arwidcool/Solder-Plate/src/thermistors/ThermistorLookup.h

#ifndef THERMISTOR_LOOKUP_H
#define THERMISTOR_LOOKUP_H

#include <Arduino.h>
#include <common.h>

struct LookupEntry
{
    uint8_t temperature;
    float value;
};

const LookupEntry lookupBottomMiddle[] = {


// {0, 1},
// {25, 1.00715513834484},
// {35, 1.12484607155925},
// {40, 1.13743718719145},
// {45, 1.13506399305814},
// {50, 1.13067636137849},
// {55, 1.11648433361902},
// {60, 1.08544627050144},
// {65, 1.08660293694492},
// {70, 1.08001421226446},
// {75, 1.16027464588806},
// {80, 1.15704474661452},
// {85, 1.1483519592037},
// {90, 1.13590936413276},
// {95, 1.11755407120932},
// {100, 1.098508196505047},
// {105, 1.1022625340138},
// {110, 1.15477823648416},
// {115, 1.07527755445145},
// {120, 1.11340733480523},
// {125, 1.11488197269303},
// {130, 1.11527719047251},
// {135, 1.11613530209391},
// {140, 1.11503246127647},
// {145, 1.11589573878646},
// {150, 1.09704724078137},
// {155, 1.07429110718977},
// {160, 1.077298663304549},
// {165, 1.06001826143415},
// {170, 1.064369457141502},
// {175, 1.077960941911383},
// {180, 1.05465186375123},
// {185, 1.04123672344689},

//  {0, 1},
// {25, 1},
// {35, 1.1052933159867},
// {40, 1.21609667854928},
// {45, 1.2911142404736},
// {50, 1.3025297616858},
// {55, 1.23009750677688},
// {60, 1.21020012832492},
// {65, 1.1958744927507},
// {70, 1.17736636429599},
// {75, 1.16148454663088},
// {80, 1.14128677245524},
// {85, 1.12056018153759},
// {90, 1.09751446890912},
// {95, 1.0719327567656},
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
    template <size_t N>
    constexpr size_t getLookupTableSize(const LookupEntry (&)[N])
    {
        return N;
    }
    float static interpolate(float x, float x0, float x1, float y0, float y1);
    uint8_t tableSize;

private:
};

#endif // THERMISTOR_LOOKUP_H
